MikeFord12/Turtle-Sweeper/VoltageReader/VoltageReader.cpp

#include "VoltageReader.h"

// returns time remaining on battery in minutes
int getBatteryTimeRemaining()
{
								return convertVrefToPercentage(getVref());
}

// Gets reference voltage based on internal arduino voltage
long getVref()
{
								// Read 1.1V reference against AVcc
								// set the reference to Vcc and the measurement to the internal 1.1V reference
		#if defined(__AVR_ATmega32U4__) || defined(__AVR_ATmega1280__) || defined(__AVR_ATmega2560__)
								ADMUX = _BV(REFS0) | _BV(MUX4) | _BV(MUX3) | _BV(MUX2) | _BV(MUX1);
		#elif defined (__AVR_ATtiny24__) || defined(__AVR_ATtiny44__) || defined(__AVR_ATtiny84__)
								ADMUX = _BV(MUX5) | _BV(MUX0);
		#elif defined (__AVR_ATtiny25__) || defined(__AVR_ATtiny45__) || defined(__AVR_ATtiny85__)
								ADMUX = _BV(MUX3) | _BV(MUX2);
		#else
								ADMUX = _BV(REFS0) | _BV(MUX3) | _BV(MUX2) | _BV(MUX1);
		#endif

								delay(2); // Wait for Vref to settle
								ADCSRA |= _BV(ADSC); // Start conversion
								while (bit_is_set(ADCSRA,ADSC)); // measuring

								uint8_t low  = ADCL;// must read ADCL first - it then locks ADCH
								uint8_t high = ADCH; // unlocks both

								long result = (high<<8) | low;

								result = 1125300L / result; // Calculate Vcc (in mV); 1125300 = 1.1*1023*1000
								return result; // Vcc in millivolts
}

// converts vref to time remaining on battery
int convertVrefToPercentage(long vref)
{
								switch(vref)
								{
								// >>> Above is red
								case 0 ... 4295: 	// 6.0v and below
																return 0;

								case 4296 ... 4387:	// 6.1v
																return 1;

								case 4388 ... 4484:	// 6.2v
																

								case 4485 ... 4584:	// 6.3v
																return 2;

								// >>> Above is yellow
								case 4585 ... 4677:	// 6.4v
																

								case 4678 ... 4777:	// 6.5v
																

								case 4778 ... 4880:	// 6.6v
																return 5;

								case 4881 ... 4988:	// 6.7v
																

								case 4989 ... 5010:	// 6.8v
																return 10;
								// >>> Above is green
								case 5011 ... LONG_MAX: // 6.9v and above
																return 100;

								default:
																return 0;
								}
}
