MikeFord12/Turtle-Sweeper/main/Globals.h

#ifndef _Globals_h
#define _Globals_h

//Program States
#define MAIN_SCREEN 1
#define DETECTION_SCREEN 2
#define GPSFIX_SCREEN 3


#define READ_MODE 4
#define WRITE_MODE 5

#define TEN_MINUTES_IN_MS 600000
#define SIX_MINUTES_IN_MS 360000
#define ONE_MINUTE_IN_MS  60000
#define THIRTY_SECONDS_IN_MS  30000
#define TWO_SECONDS_IN_MS  2000





#endif
